DeMarco/DMH-VCO-40106/DMH_VCO_40106_Firmware/DMH_VCO_40106_Firmware/Frequency_table_float.h

#define NOTE_QUANTITY	98
#define NOTE_MAX		NOTE_QUANTITY - 1
#define NOTE_MIN		8 //G#0

// [note][limits]
const float frequency_table[NOTE_QUANTITY][5] PROGMEM = {
{ 15.89		,	16.12	,	16.31	,	16.40	,	16.59	} ,	//C0
{ 16.84		,	17.08	,	17.28	,	17.38	,	17.58	} ,
{ 17.84		,	18.10	,	18.30	,	18.41	,	18.63	} ,
{ 18.90		,	19.17	,	19.39	,	19.50	,	19.73	} ,
{ 20.02		,	20.31	,	20.54	,	20.66	,	20.91	} ,
{ 21.21		,	21.52	,	21.77	,	21.89	,	22.15	} ,
{ 22.48		,	22.80	,	23.06	,	23.19	,	23.47	} ,
{ 23.81		,	24.16	,	24.43	,	24.57	,	24.86	} ,
{ 25.23		,	25.59	,	25.88	,	26.03	,	26.34	} ,
{ 26.73		,	27.11	,	27.42	,	27.58	,	27.91	} ,
{ 28.32		,	28.73	,	29.05	,	29.22	,	29.57	} ,
{ 30.00		,	30.43	,	30.78	,	30.96	,	31.33	} ,
{ 31.79		,	32.24	,	32.61	,	32.80	,	33.19	} ,	//C1
{ 33.68		,	34.16	,	34.55	,	34.75	,	35.16	} ,
{ 35.68		,	36.19	,	36.61	,	36.82	,	37.25	} ,
{ 37.80		,	38.35	,	38.78	,	39.01	,	39.47	} ,
{ 40.05		,	40.63	,	41.09	,	41.33	,	41.82	} ,
{ 42.43		,	43.04	,	43.53	,	43.78	,	44.30	} ,
{ 44.95		,	45.60	,	46.12	,	46.39	,	46.94	} ,
{ 47.62		,	48.31	,	48.86	,	49.15	,	49.73	} ,
{ 50.46		,	51.18	,	51.77	,	52.07	,	52.68	} ,
{ 53.46		,	54.23	,	54.85	,	55.16	,	55.82	} ,
{ 56.64		,	57.45	,	58.11	,	58.44	,	59.14	} ,
{ 60.00		,	60.87	,	61.56	,	61.92	,	62.65	} ,
{ 63.57		,	64.49	,	65.22	,	65.60	,	66.38	} ,	//C2
{ 67.35		,	68.32	,	69.10	,	69.50	,	70.33	} ,
{ 71.36		,	72.39	,	73.21	,	73.63	,	74.51	} ,
{ 75.60		,	76.69	,	77.56	,	78.01	,	78.94	} ,
{ 80.09		,	81.25	,	82.18	,	82.65	,	83.63	} ,
{ 84.86		,	86.08	,	87.06	,	87.57	,	88.60	} ,
{ 89.90		,	91.20	,	92.24	,	92.77	,	93.87	} ,
{ 95.25		,	96.62	,	97.72	,	98.29	,	99.46	} ,
{ 100.91	,	102.37	,	103.53	,	104.13	,	105.37	} ,
{ 106.91	,	108.46	,	109.69	,	110.33	,	111.64	} ,
{ 113.27	,	114.91	,	116.21	,	116.89	,	118.27	} ,
{ 120.01	,	121.74	,	123.12	,	123.84	,	125.31	} ,
{ 127.14	,	128.98	,	130.45	,	131.20	,	132.76	} ,	//C3
{ 134.70	,	136.65	,	138.20	,	139.00	,	140.65	} ,
{ 142.71	,	144.77	,	146.42	,	147.27	,	149.02	} ,
{ 151.20	,	153.38	,	155.13	,	156.03	,	157.88	} ,
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
};
