DeMarco/DMH-VCO-40106/DMH_VCO_40106_Firmware/DMH_VCO_40106_Firmware/Frequency_table_uint16.h

#define NOTE_QUANTITY	98
#define NOTE_MAX		NOTE_QUANTITY - 1
#define NOTE_MIN		1

// [note][limits]
const uint16_t frequency_table[NOTE_QUANTITY][5] PROGMEM = {
{ 159	,	161		,	163		,	164		,	166		} ,
{ 168	,	171		,	173		,	174		,	176		} ,
{ 178	,	181		,	183		,	184		,	186		} ,
{ 189	,	192		,	194		,	195		,	197		} ,
{ 200	,	203		,	205		,	207		,	209		} ,
{ 212	,	215		,	218		,	219		,	222		} ,
{ 225	,	228		,	231		,	232		,	235		} ,
{ 238	,	242		,	244		,	246		,	249		} ,
{ 252	,	256		,	259		,	260		,	263		} ,
{ 267	,	271		,	274		,	276		,	279		} ,
{ 283	,	287		,	291		,	292		,	296		} ,
{ 300	,	304		,	308		,	310		,	313		} ,
{ 318	,	322		,	326		,	328		,	332		} ,
{ 337	,	342		,	346		,	348		,	352		} ,
{ 357	,	362		,	366		,	368		,	373		} ,
{ 378	,	383		,	388		,	390		,	395		} ,
{ 400	,	406		,	411		,	413		,	418		} ,
{ 424	,	430		,	435		,	438		,	443		} ,
{ 450	,	456		,	461		,	464		,	469		} ,
{ 476	,	483		,	489		,	491		,	497		} ,
{ 505	,	512		,	518		,	521		,	527		} ,
{ 535	,	542		,	548		,	552		,	558		} ,
{ 566	,	575		,	581		,	584		,	591		} ,
{ 600	,	609		,	616		,	619		,	627		} ,
{ 636	,	645		,	652		,	656		,	664		} ,
{ 674	,	683		,	691		,	695		,	703		} ,
{ 714	,	724		,	732		,	736		,	745		} ,
{ 756	,	767		,	776		,	780		,	789		} ,
{ 801	,	813		,	822		,	827		,	836		} ,
{ 849	,	861		,	871		,	876		,	886		} ,
{ 899	,	912		,	922		,	928		,	939		} ,
{ 952	,	966		,	977		,	983		,	995		} ,
{ 1009	,	1024	,	1035	,	1041	,	1054	} ,
{ 1069	,	1085	,	1097	,	1103	,	1116	} ,
{ 1133	,	1149	,	1162	,	1169	,	1183	} ,
{ 1200	,	1217	,	1231	,	1238	,	1253	} ,
{ 1271	,	1290	,	1304	,	1312	,	1328	} ,
{ 1347	,	1366	,	1382	,	1390	,	1407	} ,
{ 1427	,	1448	,	1464	,	1473	,	1490	} ,
{ 1512	,	1534	,	1551	,	1560	,	1579	} ,
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
};
